yshestakov/UKNC-HDD-Suvorov/UKNC-HDD-Mod1.kicad_sch

## KiCad design UKNC-HDD-Mod1.kicad_sch (2023-04-02)

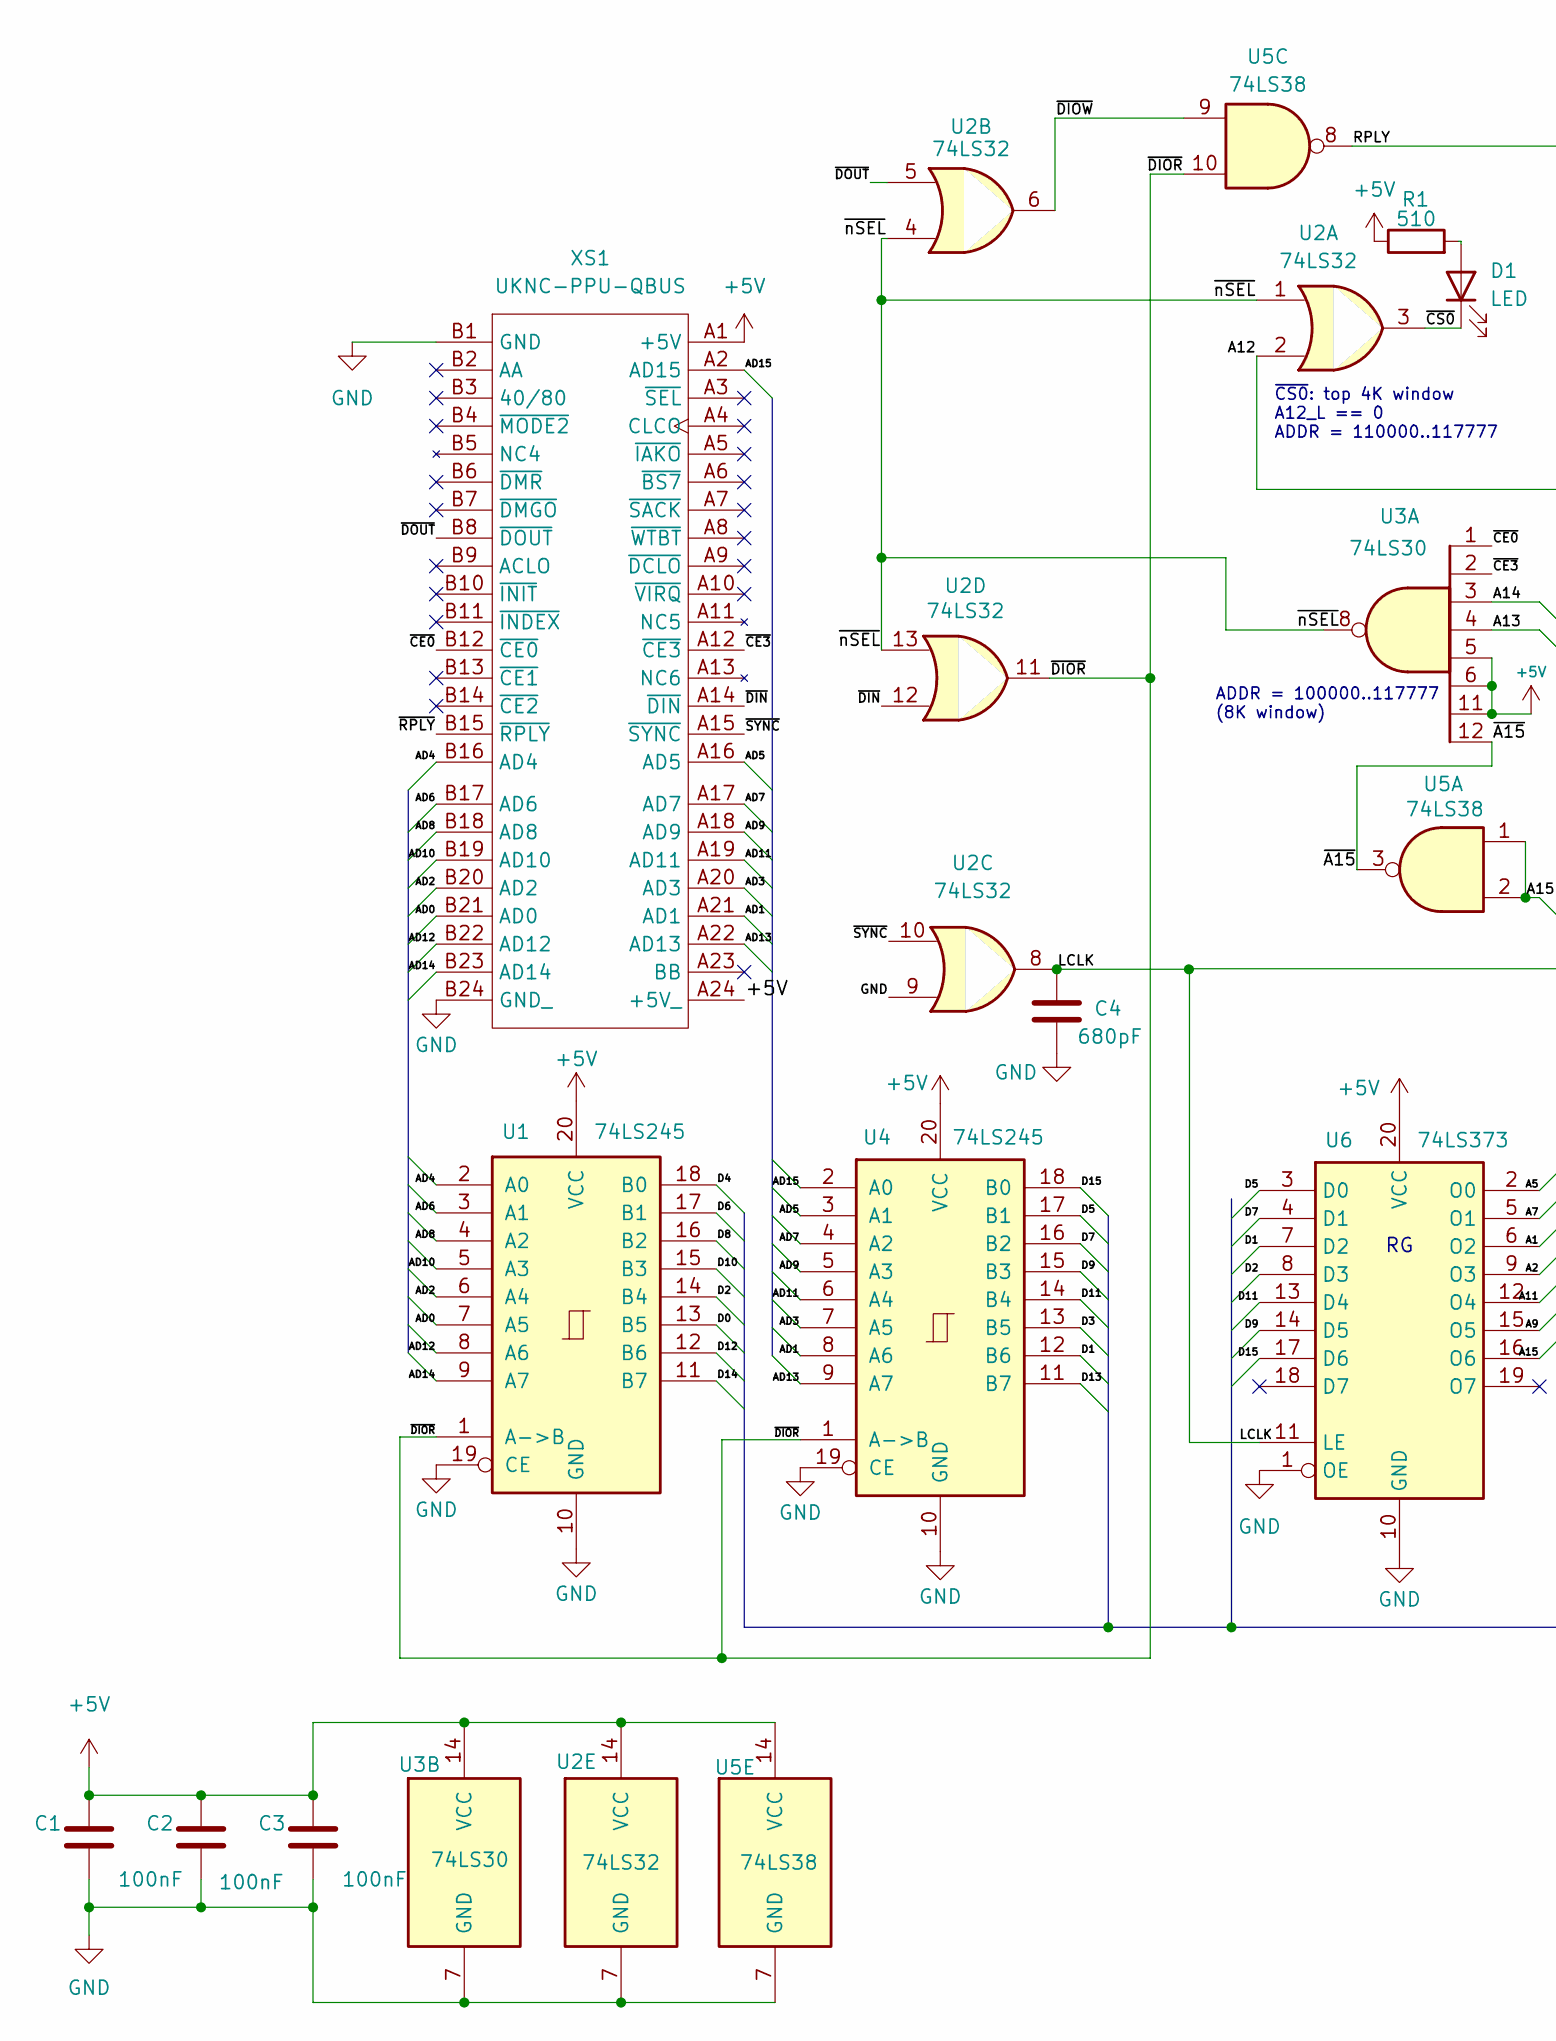
[picture p9: schematic UKNC-HDD-Mod1.kicad_sch, part in row 1, column 1]

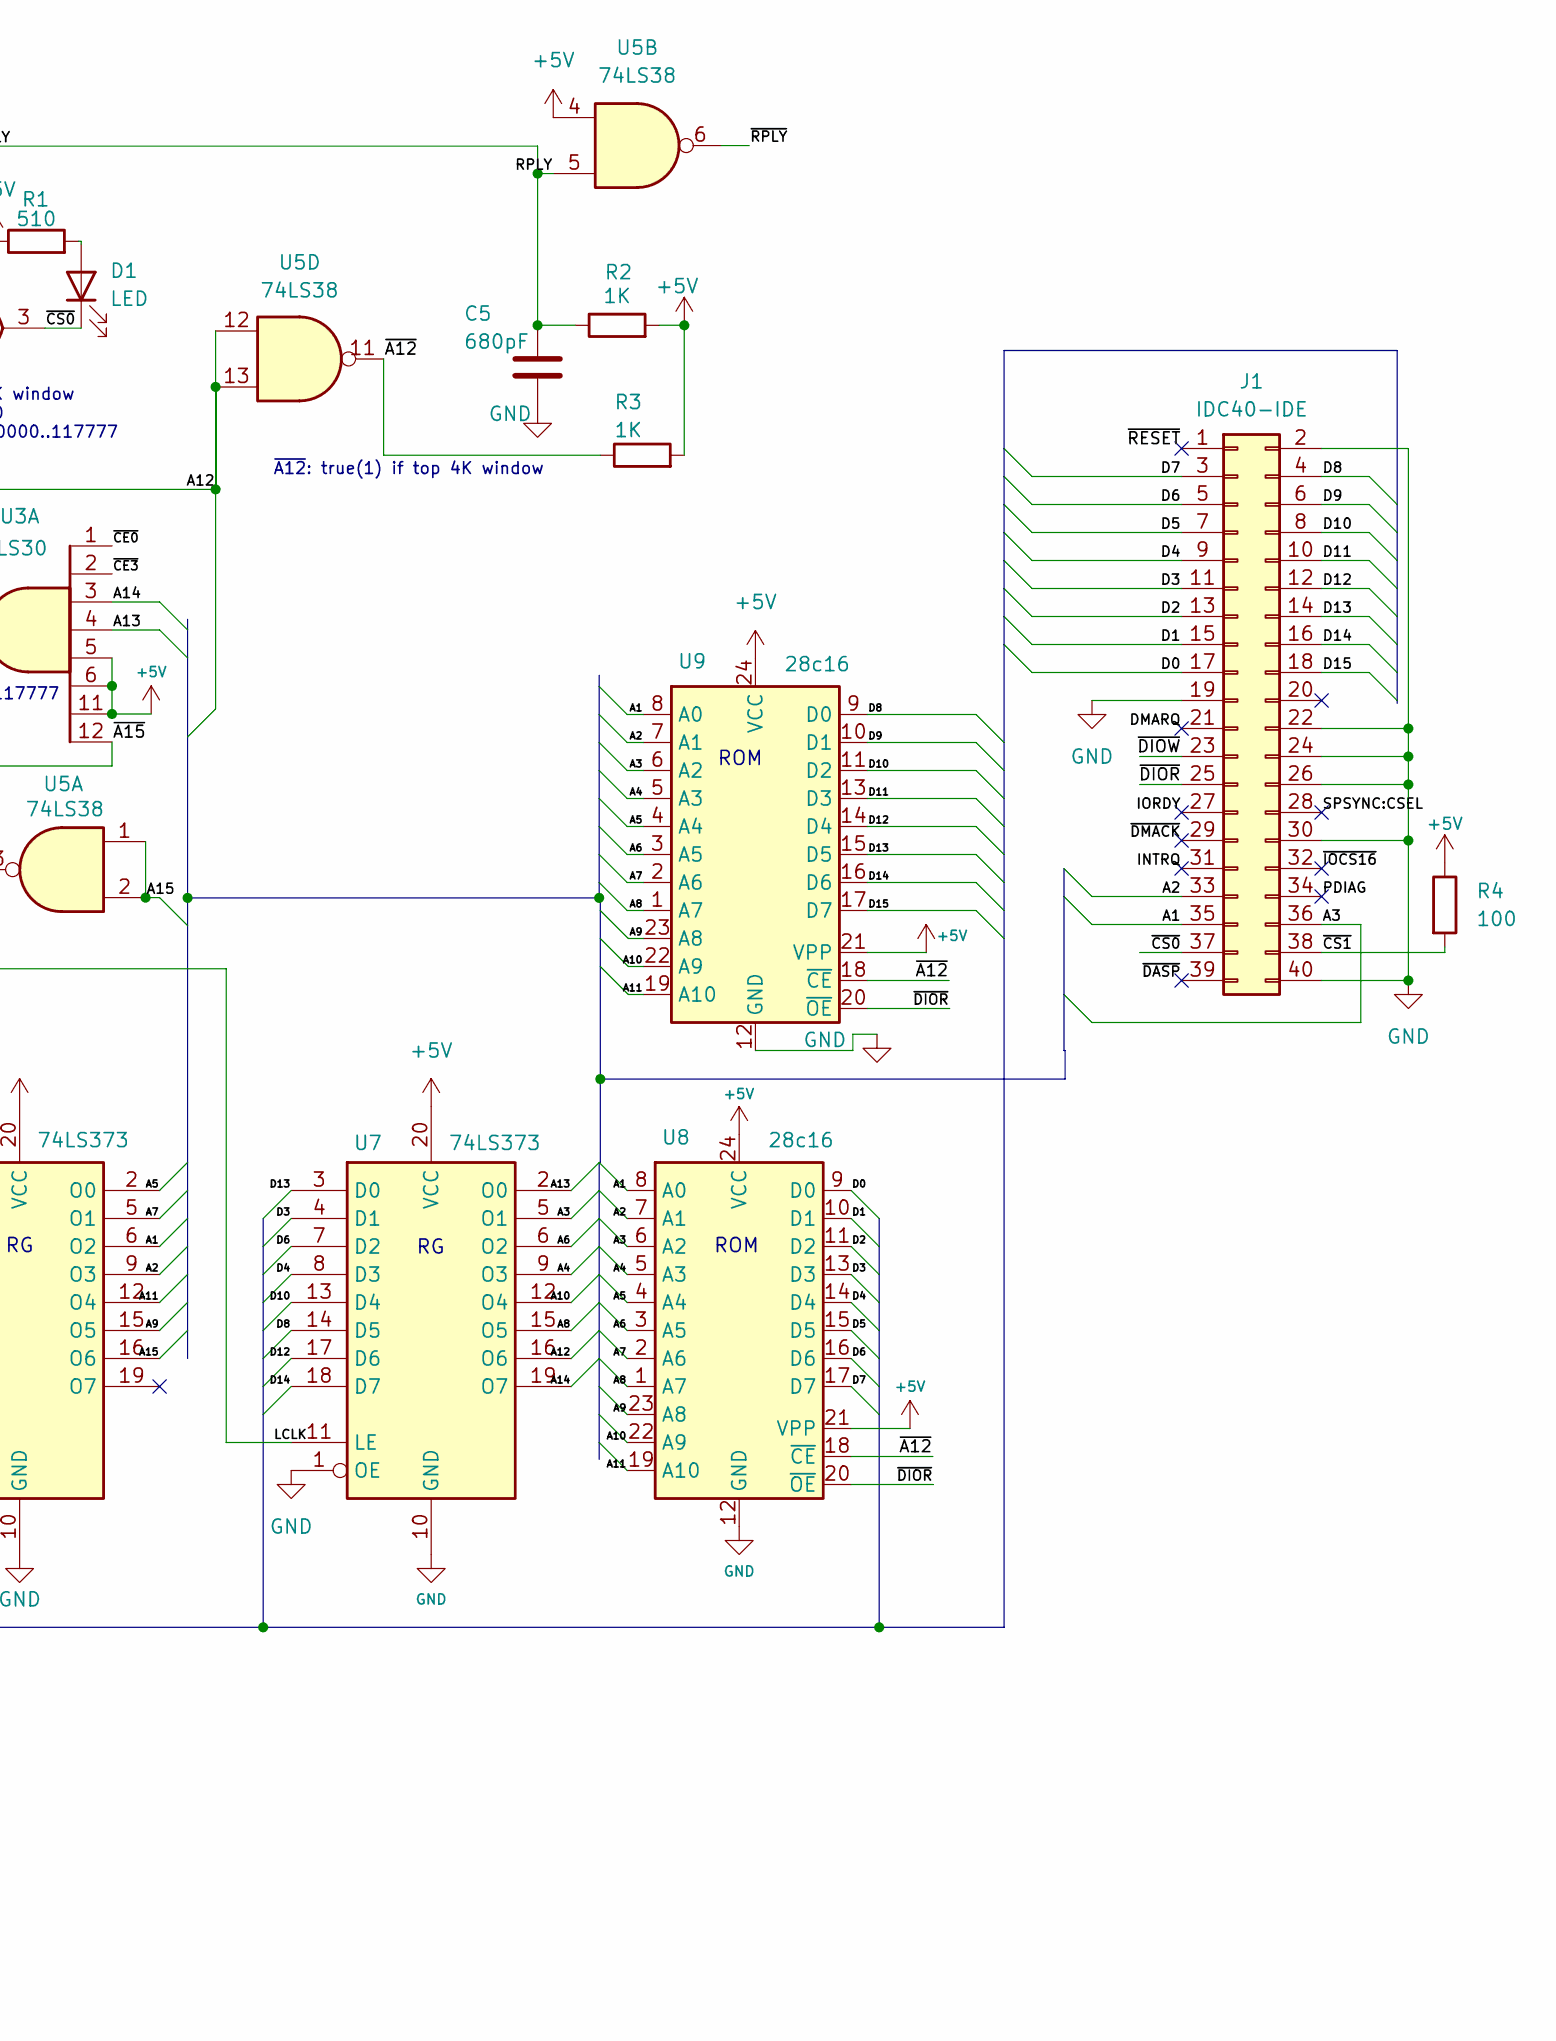
[picture p10: schematic UKNC-HDD-Mod1.kicad_sch, part in row 1, column 2]

Parts:
C1, C2: 100nF; C_0402_1005Metric; JLCPCB Part # C307331
C3: 100nF; C_0402_1005Metric; JLCPB Part # C307331
C4, C5: 680pF; C_0603_1608Metric
D1: LED; LED_0805_2012Metric
J1: IDC40-IDE; IDC-Header_2x20_P2.54mm_Horizontal
R1: 510; R_0805_2012Metric
R2, R3: 1K; R_0805_2012Metric
R4: 100; R_0805_2012Metric
U1, U4: 74LS245; DIP-20_W7.62mm
U2: 74LS32; DIP-14_W7.62mm
U3: 74LS30; DIP-14_W7.62mm
U5: 74LS38; DIP-14_W7.62mm
U6, U7: 74LS373; DIP-20_W7.62mm
U8, U9: 28c16; DIP-24_W15.24mm
XS1: UKNC-PPU-QBUS; SNP15-48-BOARD

Connections:
+5V: C1.1, C2.1, C3.1, R1.1, R2.2, R3.2, R4.1, U1.20 (VCC), U2.14 (VCC), U3.5, U3.6, U3.11, U3.14 (VCC), U4.20 (VCC), U5.4, U5.14 (VCC), U6.20 (VCC), U7.20 (VCC), U8.21 (VPP), U8.24 (VCC), U9.21 (VPP), U9.24 (VCC), XS1.A1 (+5V), XS1.A24 (+5V_)
A1: J1.35, U6.6 (O2), U8.8 (A0), U9.8 (A0)
A2: J1.33, U6.9 (O3), U8.7 (A1), U9.7 (A1)
A3: J1.36, U7.5 (O1), U8.6 (A2), U9.6 (A2)
A4: U7.9 (O3), U8.5 (A3), U9.5 (A3)
A5: U6.2 (O0), U8.4 (A4), U9.4 (A4)
A6: U7.6 (O2), U8.3 (A5), U9.3 (A5)
A7: U6.5 (O1), U8.2 (A6), U9.2 (A6)
A8: U7.15 (O5), U8.1 (A7), U9.1 (A7)
A9: U6.15 (O5), U8.23 (A8), U9.23 (A8)
A10: U7.12 (O4), U8.22 (A9), U9.22 (A9)
A11: U6.12 (O4), U8.19 (A10), U9.19 (A10)
A12: U2.2, U5.12, U5.13, U7.16 (O6)
A13: U3.4, U7.2 (O0)
A14: U3.3, U7.19 (O7)
A15: U5.1, U5.2, U6.16 (O6)
AD0: U1.7 (A5), XS1.B21 (AD0)
AD1: U4.8 (A6), XS1.A21 (AD1)
AD2: U1.6 (A4), XS1.B20 (AD2)
AD3: U4.7 (A5), XS1.A20 (AD3)
AD4: U1.2 (A0), XS1.B16 (AD4)
AD5: U4.3 (A1), XS1.A16 (AD5)
AD6: U1.3 (A1), XS1.B17 (AD6)
AD7: U4.4 (A2), XS1.A17 (AD7)
AD8: U1.4 (A2), XS1.B18 (AD8)
AD9: U4.5 (A3), XS1.A18 (AD9)
AD10: U1.5 (A3), XS1.B19 (AD10)
AD11: U4.6 (A4), XS1.A19 (AD11)
AD12: U1.8 (A6), XS1.B22 (AD12)
AD13: U4.9 (A7), XS1.A22 (AD13)
AD14: U1.9 (A7), XS1.B23 (AD14)
AD15: U4.2 (A0), XS1.A2 (AD15)
D0: J1.17, U1.13 (B5), U8.9 (D0)
D1: J1.15, U4.12 (B6), U6.7 (D2), U8.10 (D1)
D2: J1.13, U1.14 (B4), U6.8 (D3), U8.11 (D2)
D3: J1.11, U4.13 (B5), U7.4 (D1), U8.13 (D3)
D4: J1.9, U1.18 (B0), U7.8 (D3), U8.14 (D4)
D5: J1.7, U4.17 (B1), U6.3 (D0), U8.15 (D5)
D6: J1.5, U1.17 (B1), U7.7 (D2), U8.16 (D6)
D7: J1.3, U4.16 (B2), U6.4 (D1), U8.17 (D7)
D8: J1.4, U1.16 (B2), U7.14 (D5), U9.9 (D0)
D9: J1.6, U4.15 (B3), U6.14 (D5), U9.10 (D1)
D10: J1.8, U1.15 (B3), U7.13 (D4), U9.11 (D2)
D11: J1.10, U4.14 (B4), U6.13 (D4), U9.13 (D3)
D12: J1.12, U1.12 (B6), U7.17 (D6), U9.14 (D4)
D13: J1.14, U4.11 (B7), U7.3 (D0), U9.15 (D5)
D14: J1.16, U1.11 (B7), U7.18 (D7), U9.16 (D6)
D15: J1.18, U4.18 (B0), U6.17 (D6), U9.17 (D7)
DMARQ: J1.21
GND: C1.2, C2.2, C3.2, C4.2, C5.2, J1.2, J1.19, J1.22, J1.24, J1.26, J1.30, J1.40, U1.10 (GND), U1.19 (CE), U2.7 (GND), U2.9, U3.7 (GND), U4.10 (GND), U4.19 (CE), U5.7 (GND), U6.1 (OE), U6.10 (GND), U7.1 (OE), U7.10 (GND), U8.12 (GND), U9.12 (GND), XS1.B1 (GND), XS1.B24 (GND_)
INTRQ: J1.31
IORDY: J1.27
LCLK: C4.1, U2.8, U6.11 (LE), U7.11 (LE)
unnamed: D1.2 (A), R1.2
PDIAG: J1.34
RPLY: C5.1, R2.1, U5.5, U5.8
SPSYNC:CSEL: J1.28
~A12: R3.1, U5.11, U8.18 (~CE), U9.18 (~CE)
~A15: U3.12, U5.3
~CE0: U3.1, XS1.B12 (~CE0)
~CE3: U3.2, XS1.A12 (~CE3)
~CS0: D1.1 (K), J1.37, U2.3
~CS1: J1.38, R4.2
~DASP: J1.39
~DIN: U2.12, XS1.A14 (~DIN)
~DIOR: J1.25, U1.1 (A->B), U2.11, U4.1 (A->B), U5.10, U8.20 (~OE), U9.20 (~OE)
~DIOW: J1.23, U2.6, U5.9
~DMACK: J1.29
~DOUT: U2.5, XS1.B8 (~DOUT)
~IOCS16: J1.32
~RESET: J1.1
~RPLY: U5.6, XS1.B15 (~RPLY)
~SYNC: U2.10, XS1.A15 (~SYNC)
~nSEL: U2.1, U2.4, U2.13, U3.8

Notes on the sheet:
~{A12}: true(1) if top 4K window
ROM
ADDR = 100000..117777 (8K window)
~{CS0}: top 4K window A12_L == 0 ADDR = 110000..117777
